AlicDanclic/ChinoHub/Software/ChinoHuB/Sys/Binary_Hex_Macros.h

#ifndef BINARY_HEX_MACROS_H
#define BINARY_HEX_MACROS_H

// 1位二进制数对应十六进制值
#define _0b0 0x0
#define _0b1 0x1

// 2位二进制数对应十六进制值
#define _0b00 0x0
#define _0b01 0x1
#define _0b10 0x2
#define _0b11 0x3

// 3位二进制数对应十六进制值
#define _0b000 0x0
#define _0b001 0x1
#define _0b010 0x2
#define _0b011 0x3
#define _0b100 0x4
#define _0b101 0x5
#define _0b110 0x6
#define _0b111 0x7

// 4位二进制数对应十六进制值
#define _0b0000 0x0
#define _0b0001 0x1
#define _0b0010 0x2
#define _0b0011 0x3
#define _0b0100 0x4
#define _0b0101 0x5
#define _0b0110 0x6
#define _0b0111 0x7
#define _0b1000 0x8
#define _0b1001 0x9
#define _0b1010 0xA
#define _0b1011 0xB
#define _0b1100 0xC
#define _0b1101 0xD
#define _0b1110 0xE
#define _0b1111 0xF

//5位二进制数对应十六进制值
#define _0b00000 0x00
#define _0b00001 0x01
#define _0b00010 0x02
#define _0b00011 0x03
#define _0b00100 0x04
#define _0b00101 0x05
#define _0b00110 0x06
#define _0b00111 0x07
#define _0b01000 0x08
#define _0b01001 0x09
#define _0b01010 0x0A
#define _0b01011 0x0B
#define _0b01100 0x0C
#define _0b01101 0x0D
#define _0b01110 0x0E
#define _0b01111 0x0F
#define _0b10000 0x10
#define _0b10001 0x11
#define _0b10010 0x12
#define _0b10011 0x13
#define _0b10100 0x14
#define _0b10101 0x15
#define _0b10110 0x16
#define _0b10111 0x17
#define _0b11000 0x18
#define _0b11001 0x19
#define _0b11010 0x1A
#define _0b11011 0x1B
#define _0b11100 0x1C
#define _0b11101 0x1D
#define _0b11110 0x1E
#define _0b11111 0x1F

//6位二进制数对应十六进制值
#define _0b000000 0x00
#define _0b000001 0x01
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
#define _0b01100111 0x67
#define _0b01101000 0x68
#define _0b01101001 0x69
#define _0b01101010 0x6A
#define _0b01101011 0x6B
#define _0b01101100 0x6C
#define _0b01101101 0x6D
#define _0b01101110 0x6E
#define _0b01101111 0x6F
#define _0b01110000 0x70
#define _0b01110001 0x71
#define _0b01110010 0x72
#define _0b01110011 0x73
#define _0b01110100 0x74
#define _0b01110101 0x75
#define _0b01110110 0x76
#define _0b01110111 0x77
#define _0b01111000 0x78
#define _0b01111001 0x79
#define _0b01111010 0x7A
#define _0b01111011 0x7B
#define _0b01111100 0x7C
#define _0b01111101 0x7D
#define _0b01111110 0x7E
#define _0b01111111 0x7F
#define _0b10000000 0x80
#define _0b10000001 0x81
#define _0b10000010 0x82
#define _0b10000011 0x83
#define _0b10000100 0x84
#define _0b10000101 0x85
#define _0b10000110 0x86
#define _0b10000111 0x87
#define _0b10001000 0x88
#define _0b10001001 0x89
#define _0b10001010 0x8A
#define _0b10001011 0x8B
#define _0b10001100 0x8C
#define _0b10001101 0x8D
#define _0b10001110 0x8E
#define _0b10001111 0x8F
#define _0b10010000 0x90
#define _0b10010001 0x91
#define _0b10010010 0x92
#define _0b10010011 0x93
#define _0b10010100 0x94
#define _0b10010101 0x95
#define _0b10010110 0x96
#define _0b10010111 0x97
#define _0b10011000 0x98
#define _0b10011001 0x99
#define _0b10011010 0x9A
#define _0b10011011 0x9B
#define _0b10011100 0x9C
#define _0b10011101 0x9D
#define _0b10011110 0x9E
#define _0b10011111 0x9F
#define _0b10100000 0xA0
#define _0b10100001 0xA1
#define _0b10100010 0xA2
#define _0b10100011 0xA3
#define _0b10100100 0xA4
#define _0b10100101 0xA5
#define _0b10100110 0xA6
#define _0b10100111 0xA7
#define _0b10101000 0xA8
#define _0b10101001 0xA9
#define _0b10101010 0xAA
#define _0b10101011 0xAB
#define _0b10101100 0xAC
#define _0b10101101 0xAD
#define _0b10101110 0xAE
#define _0b10101111 0xAF
#define _0b10110000 0xB0
#define _0b10110001 0xB1
#define _0b10110010 0xB2
#define _0b10110011 0xB3
#define _0b10110100 0xB4
#define _0b10110101 0xB5
#define _0b10110110 0xB6
#define _0b10110111 0xB7
#define _0b10111000 0xB8
#define _0b10111001 0xB9
#define _0b10111010 0xBA
#define _0b10111011 0xBB
#define _0b10111100 0xBC
#define _0b10111101 0xBD
#define _0b10111110 0xBE
#define _0b10111111 0xBF
#define _0b11000000 0xC0
#define _0b11000001 0xC1
#define _0b11000010 0xC2
#define _0b11000011 0xC3
#define _0b11000100 0xC4
#define _0b11000101 0xC5
#define _0b11000110 0xC6
#define _0b11000111 0xC7
#define _0b11001000 0xC8
#define _0b11001001 0xC9
#define _0b11001010 0xCA
#define _0b11001011 0xCB
#define _0b11001100 0xCC
#define _0b11001101 0xCD
#define _0b11001110 0xCE
#define _0b11001111 0xCF
#define _0b11010000 0xD0
#define _0b11010001 0xD1
#define _0b11010010 0xD2
#define _0b11010011 0xD3
#define _0b11010100 0xD4
#define _0b11010101 0xD5
#define _0b11010110 0xD6
#define _0b11010111 0xD7
#define _0b11011000 0xD8
#define _0b11011001 0xD9
#define _0b11011010 0xDA
#define _0b11011011 0xDB
#define _0b11011100 0xDC
#define _0b11011101 0xDD
#define _0b11011110 0xDE
#define _0b11011111 0xDF
#define _0b11100000 0xE0
#define _0b11100001 0xE1
#define _0b11100010 0xE2
#define _0b11100011 0xE3
#define _0b11100100 0xE4
#define _0b11100101 0xE5
#define _0b11100110 0xE6
#define _0b11100111 0xE7
#define _0b11101000 0xE8
#define _0b11101001 0xE9
#define _0b11101010 0xEA
#define _0b11101011 0xEB
#define _0b11101100 0xEC
#define _0b11101101 0xED
#define _0b11101110 0xEE
#define _0b11101111 0xEF
#define _0b11110000 0xF0
#define _0b11110001 0xF1
#define _0b11110010 0xF2
#define _0b11110011 0xF3
#define _0b11110100 0xF4
#define _0b11110101 0xF5
#define _0b11110110 0xF6
#define _0b11110111 0xF7
#define _0b11111000 0xF8
#define _0b11111001 0xF9
#define _0b11111010 0xFA
#define _0b11111011 0xFB
#define _0b11111100 0xFC
#define _0b11111101 0xFD
#define _0b11111110 0xFE
#define _0b11111111 0xFF

#endif // BINARY_HEX_MACROS_H
